BeardyMike/tukii/desktop client/data/image/img.png

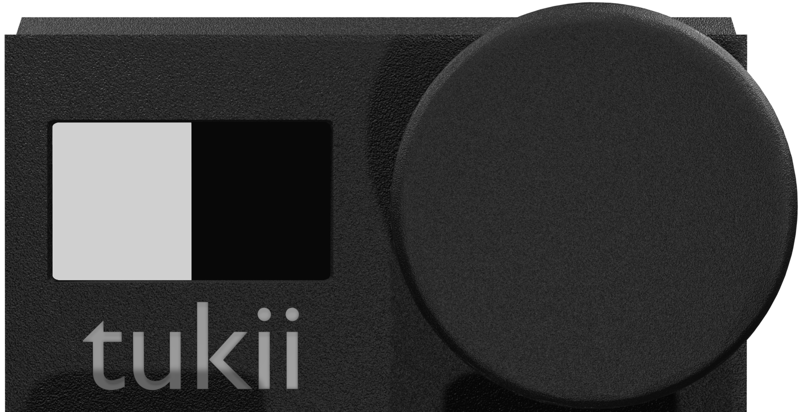
desktop client/data/image/img.png
